hexeguitar/Teensy40_SDIO_adapter/T40_SDcard_V2.kicad_sch

## KiCad design T40_SDcard_V2.kicad_sch (2024-11-08)

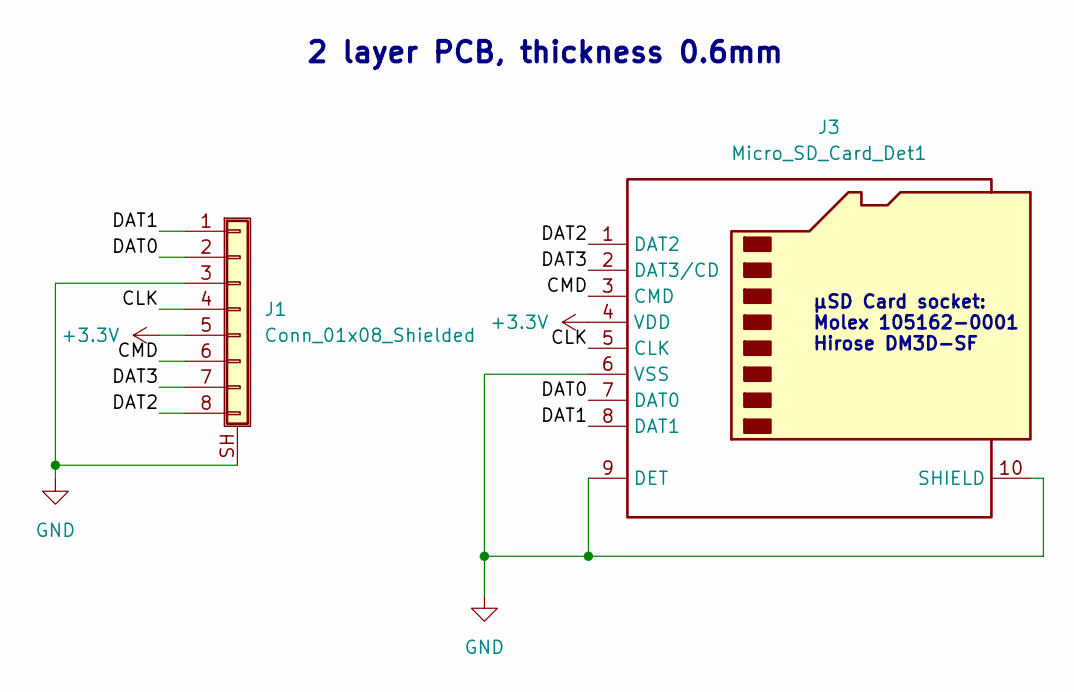
[picture p6: schematic T40_SDcard_V2.kicad_sch]

Parts:
J1: Conn_01x08_Shielded; HFW8R-1STE1H1LF_1x8_P1.0mm_FPC_THT
J3: Micro_SD_Card_Det1; MicroSD_DM3D-SF_Hirose

Connections:
+3.3V: J1.5, J3.4 (VDD)
CLK: J1.4, J3.5 (CLK)
CMD: J1.6, J3.3 (CMD)
DAT0: J1.2, J3.7 (DAT0)
DAT1: J1.1, J3.8 (DAT1)
DAT2: J1.8, J3.1 (DAT2)
DAT3: J1.7, J3.2 (DAT3/CD)
GND: J1.3, J1.SH (Shield), J3.6 (VSS), J3.9 (DET), J3.10 (SHIELD)

Notes on the sheet:
2 layer PCB, thickness 0.6mm
µSD Card socket: Molex 105162-0001 Hirose DM3D-SF
